McOrts/jaleometro/data/1002 Llogeta 7.jpeg

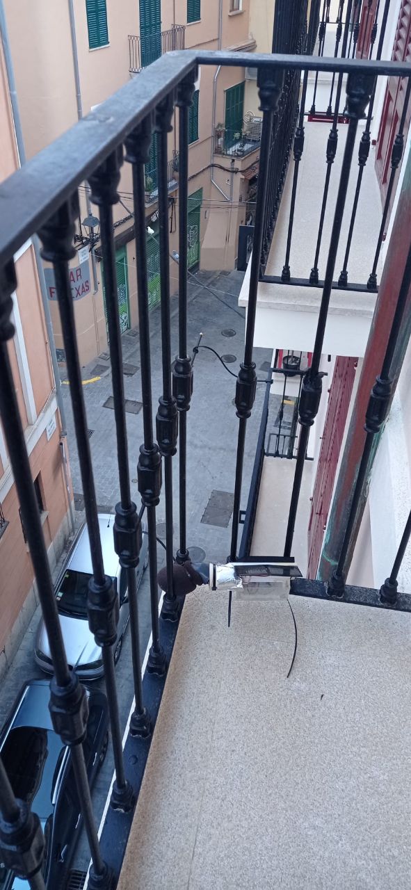
data/1002 Llogeta 7.jpeg
