McOrts/jaleometro/data/1004 Corderia 15-5_2.jpeg

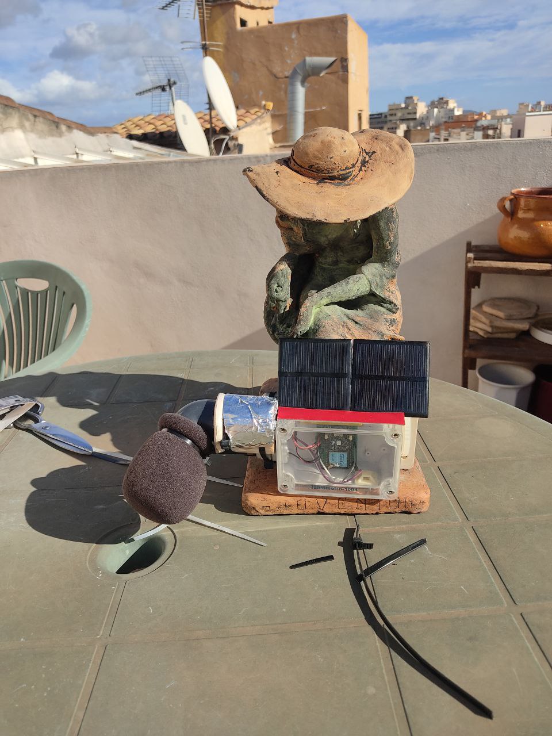
data/1004 Corderia 15-5_2.jpeg
