McOrts/jaleometro/data/1004 Corderia 15-5_3.jpeg

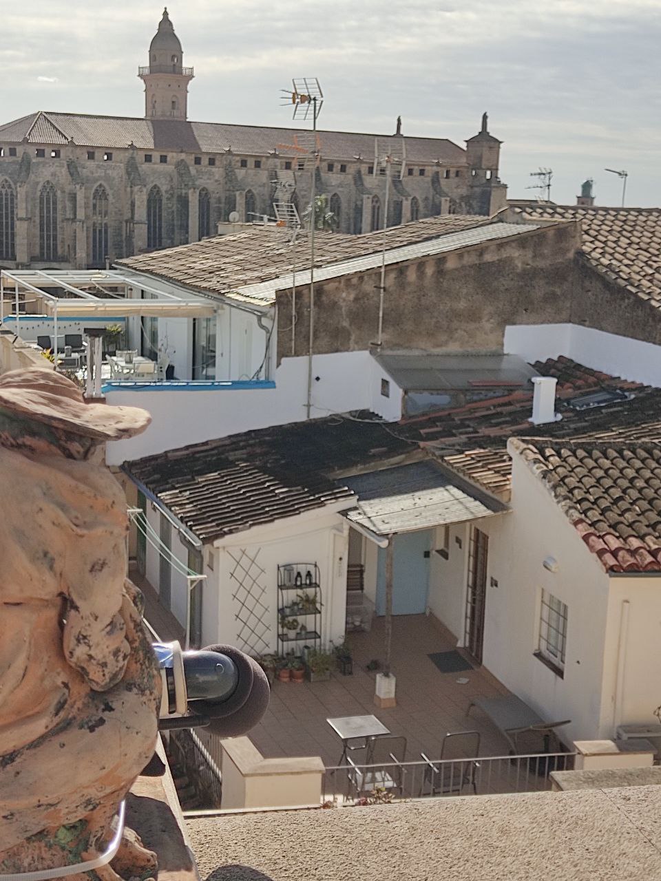
data/1004 Corderia 15-5_3.jpeg
