McOrts/jaleometro/data/1006 Cordería 15-1.jpeg

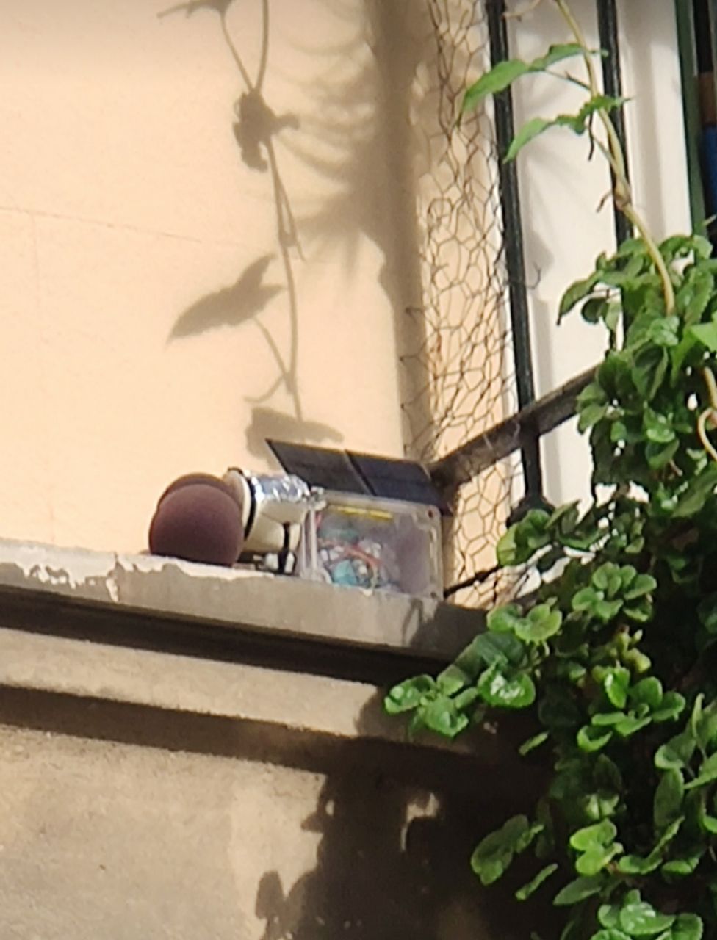
data/1006 Cordería 15-1.jpeg
