McOrts/jaleometro/data/1006 Cordería 15-1_2 copy.png

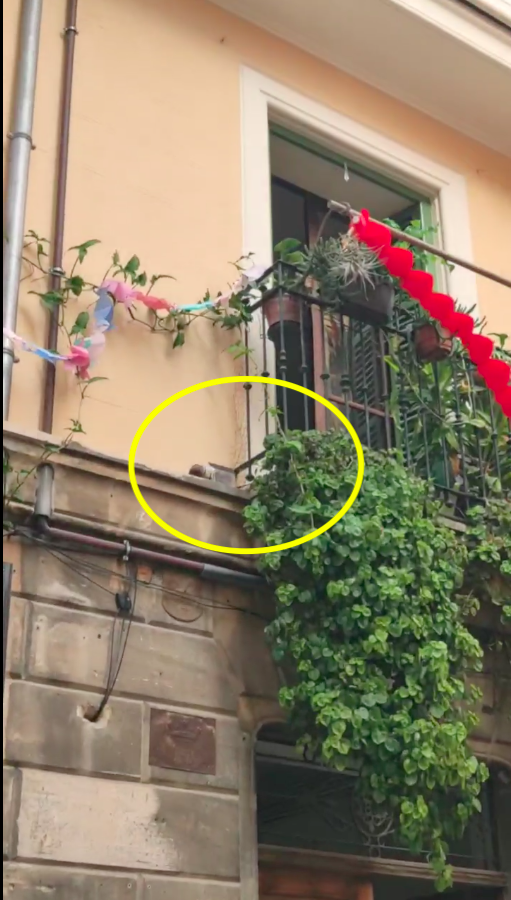
data/1006 Cordería 15-1_2 copy.png
