McOrts/jaleometro/doc/Microphone_Capsule_CEM-C9745JAD462P2.jpeg

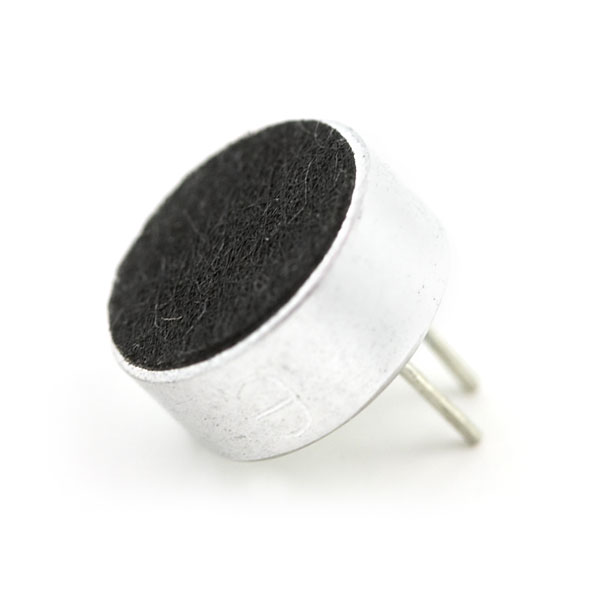
doc/Microphone_Capsule_CEM-C9745JAD462P2.jpeg
