McOrts/jaleometro/doc/MicrophoneWindscreen_foam .png

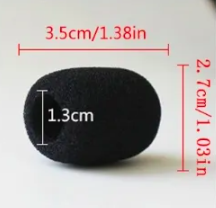
doc/MicrophoneWindscreen_foam .png
