McOrts/jaleometro/img/676x380.webp

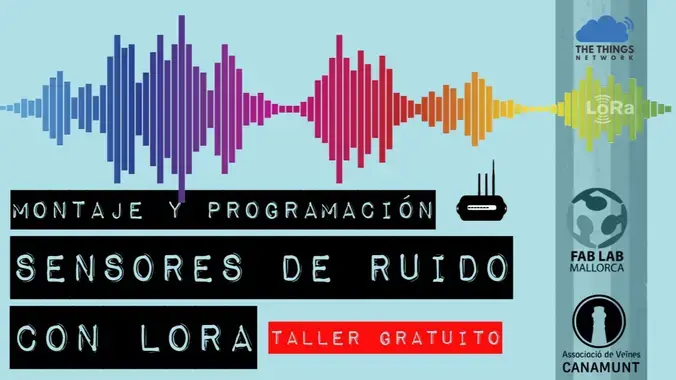
img/676x380.webp
