McOrts/jaleometro/img/1116.jpg

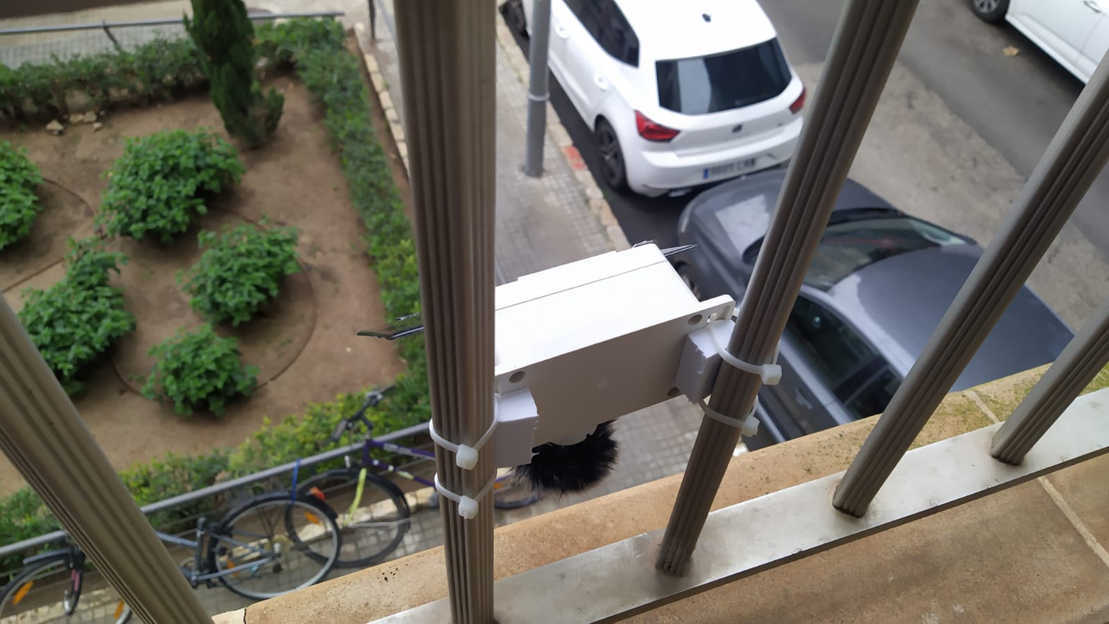
img/1116.jpg
