McOrts/jaleometro/img/canamunt_basemap.jpg

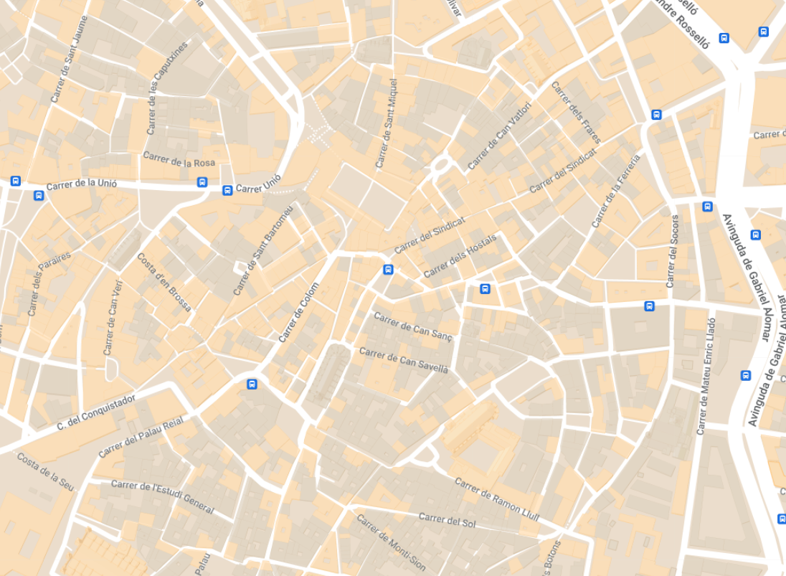
img/canamunt_basemap.jpg
