McOrts/jaleometro/img/DesviacionTipica.png

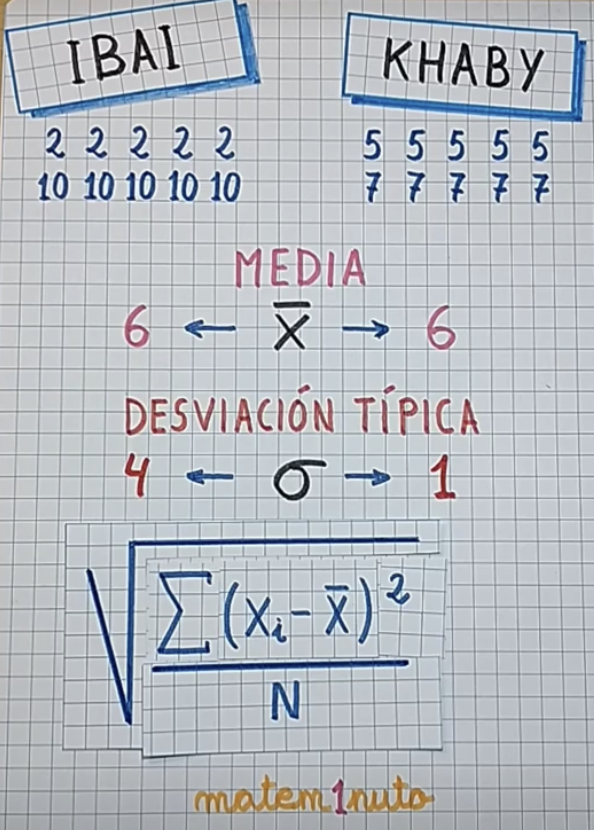
img/DesviacionTipica.png
