McOrts/jaleometro/img/How-Loud-Is-50-Decibels.jpg

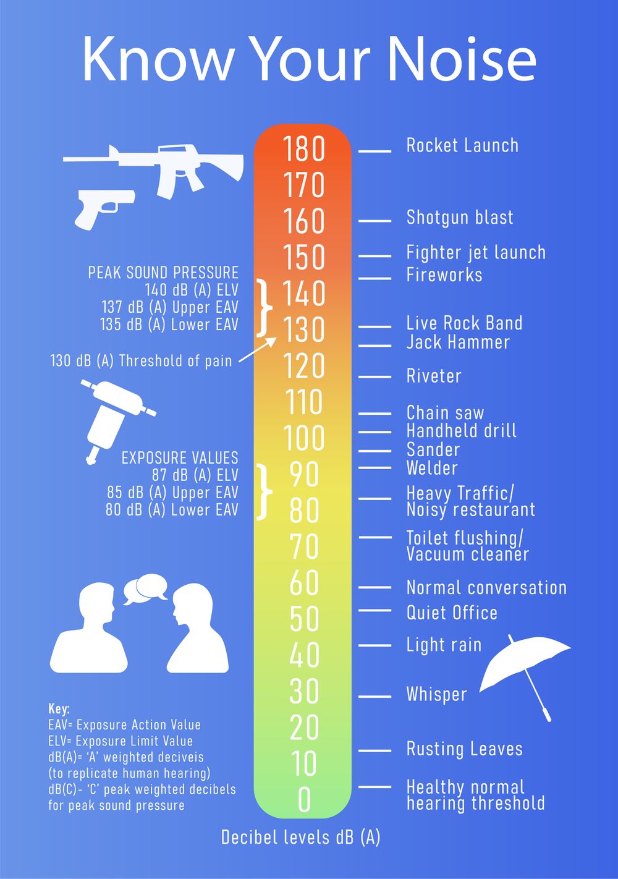
img/How-Loud-Is-50-Decibels.jpg
