McOrts/jaleometro/img/HTCC-AB01.png

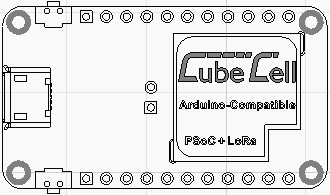
img/HTCC-AB01.png
