McOrts/jaleometro/img/IMG_3713.jpg

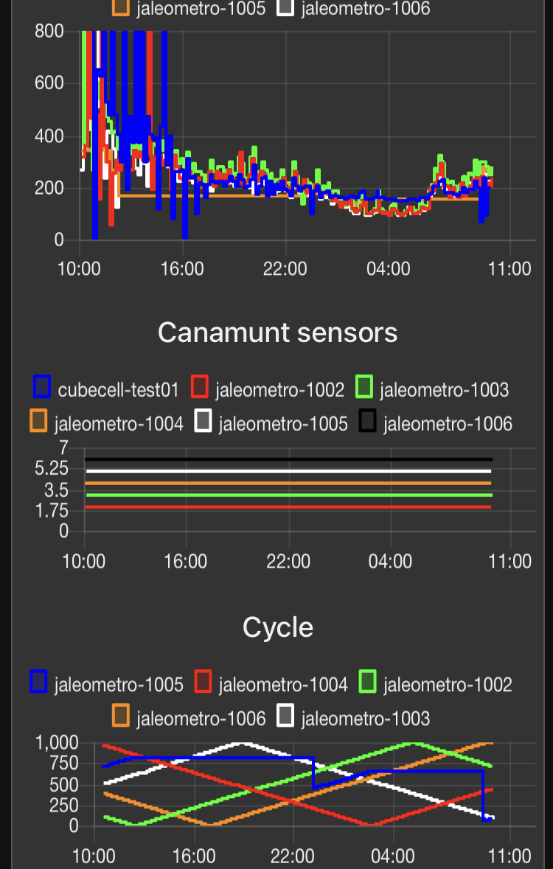
img/IMG_3713.jpg
