McOrts/jaleometro/img/jaleometro_0.jpg

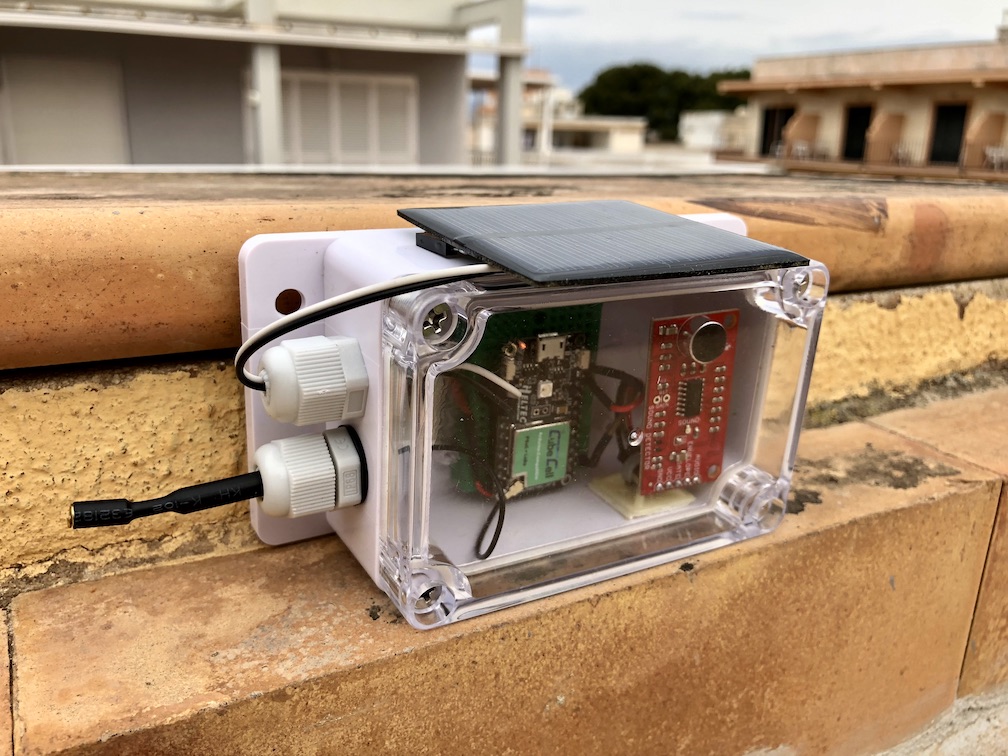
img/jaleometro_0.jpg
