McOrts/jaleometro/img/jaleometro_1.png

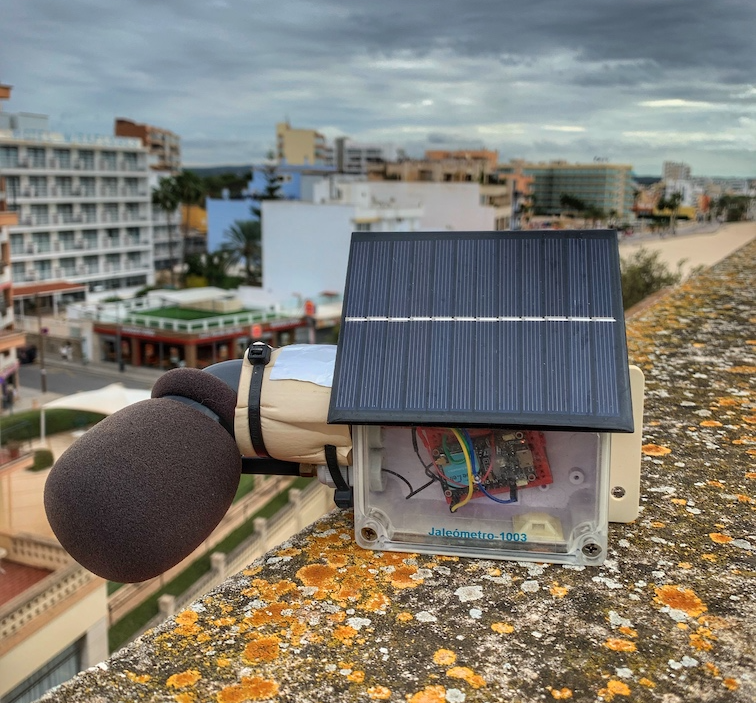
img/jaleometro_1.png
