McOrts/jaleometro/img/Jaleometro_1108.jpeg

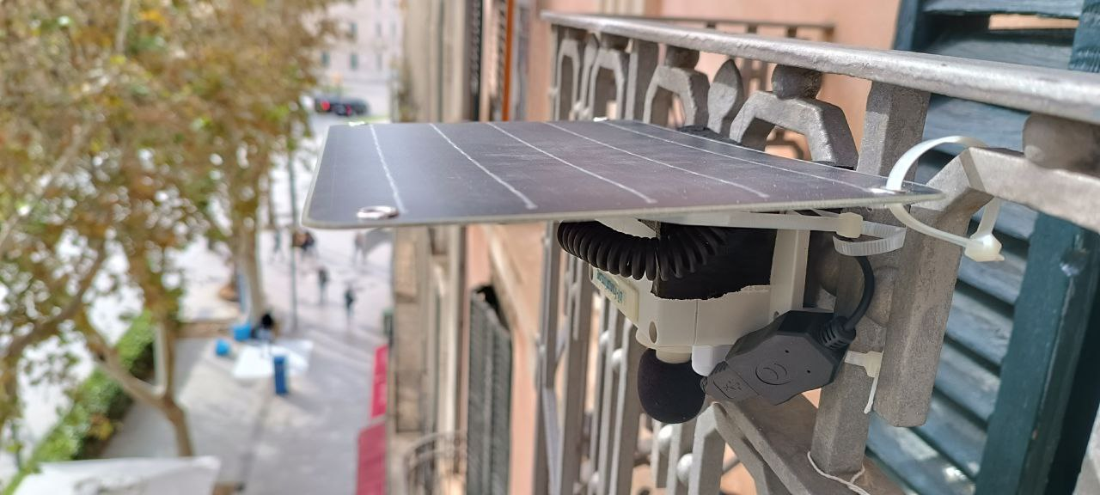
img/Jaleometro_1108.jpeg
