McOrts/jaleometro/img/JaleometroCollage.jpeg

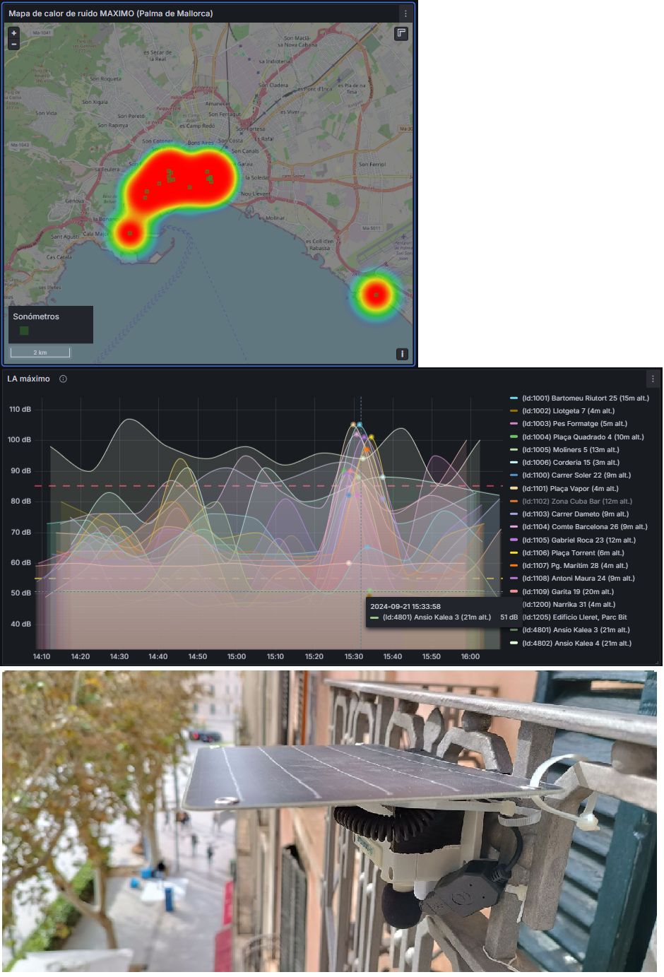
img/JaleometroCollage.jpeg
