McOrts/jaleometro/img/jaleometros_1.jpg

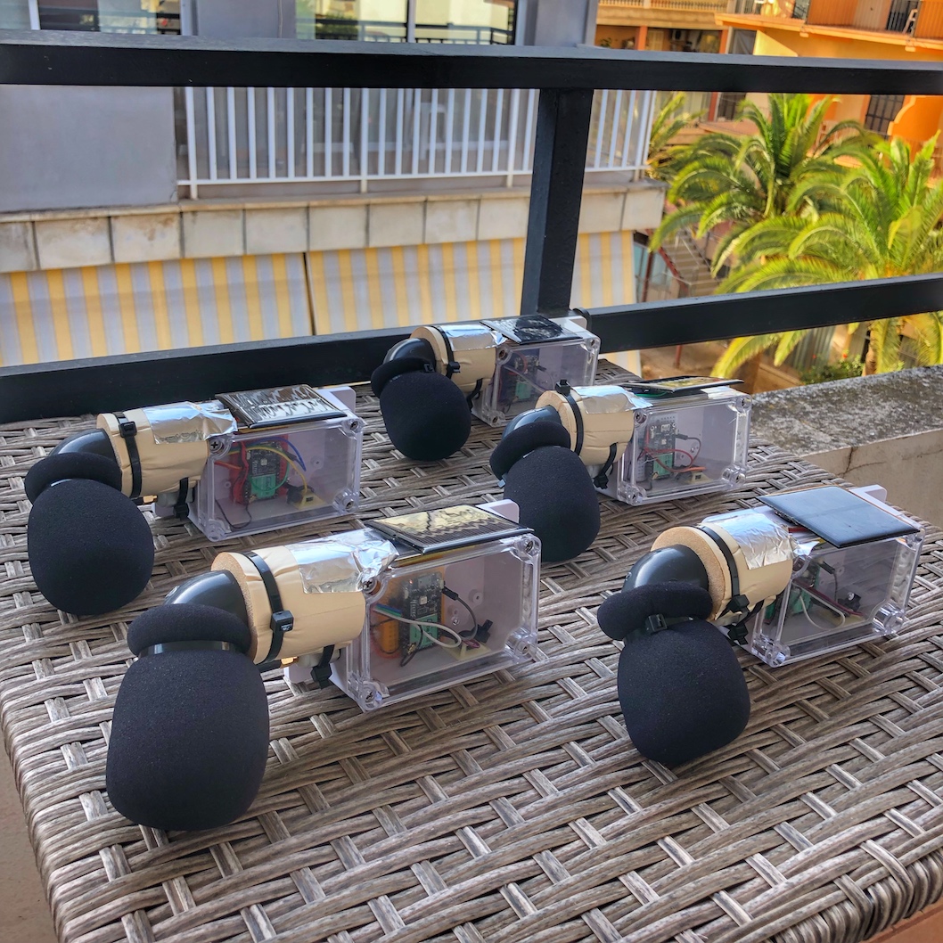
img/jaleometros_1.jpg
