McOrts/jaleometro/img/Jaleómetro_1200.jpg

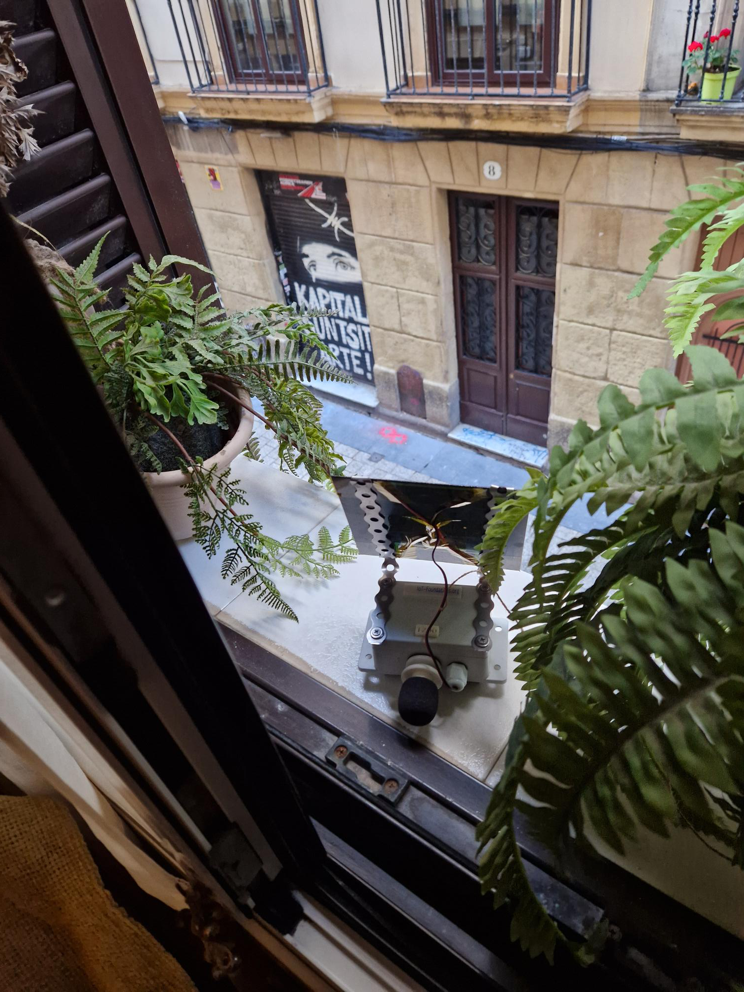
img/Jaleómetro_1200.jpg
