McOrts/jaleometro/img/TTN_device_OTAA.png

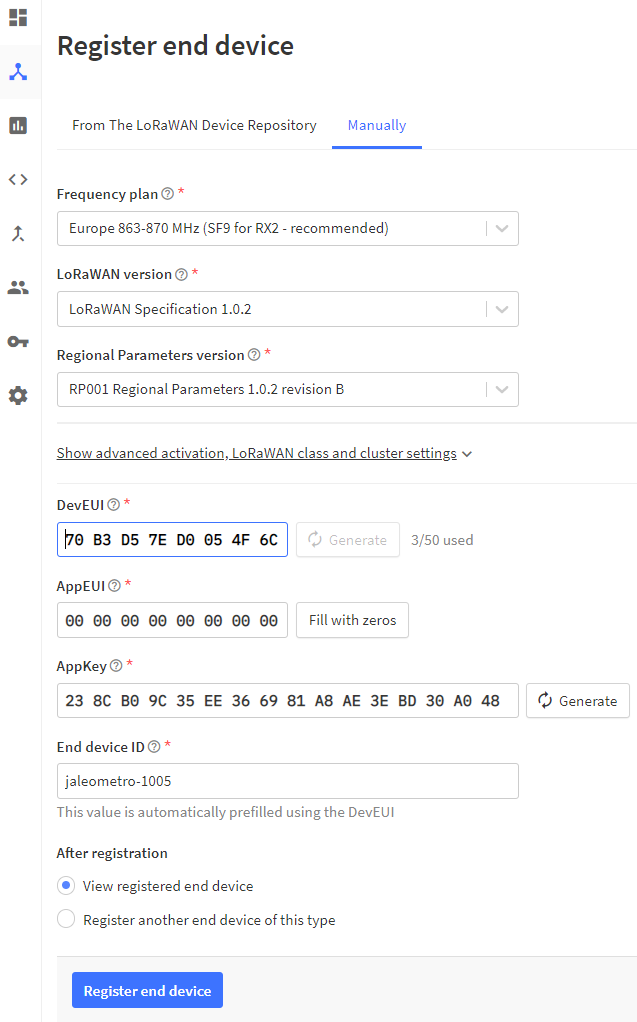
img/TTN_device_OTAA.png
