McOrts/jaleometro/news/8eed3acc-b989-45af-b673-5e21465e44ad.jpeg

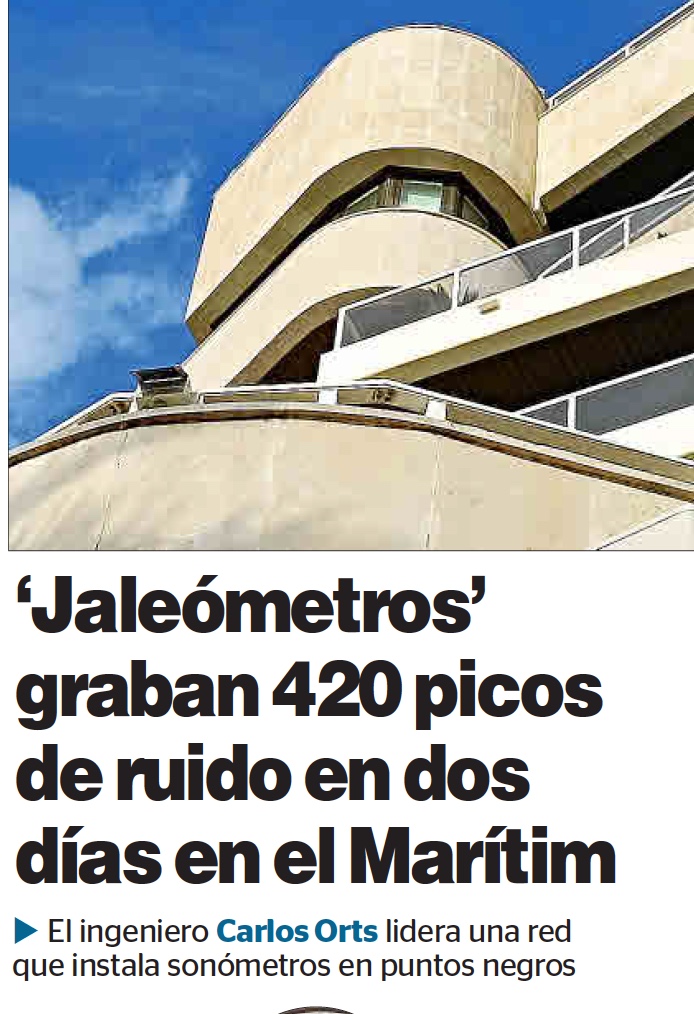
news/8eed3acc-b989-45af-b673-5e21465e44ad.jpeg
