McOrts/jaleometro/news/9c517f6d-d2a7-4473-ad57-f0665915687a.jpeg

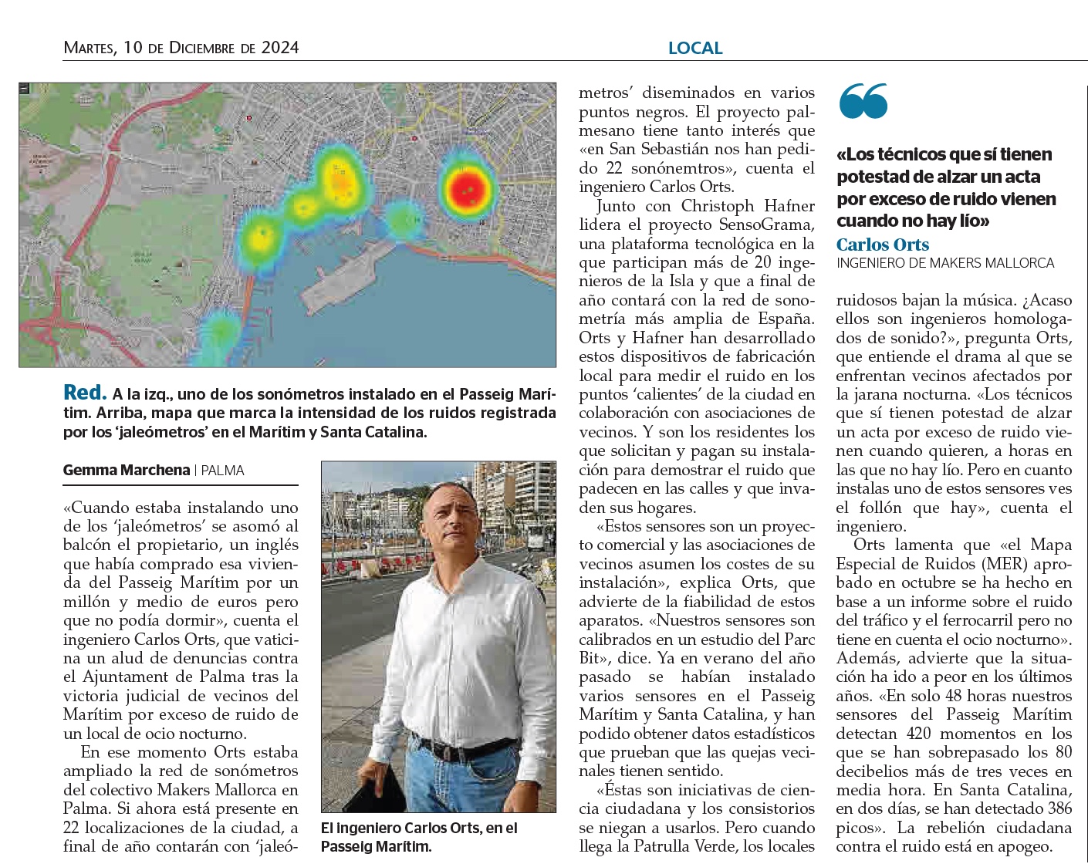
news/9c517f6d-d2a7-4473-ad57-f0665915687a.jpeg
