McOrts/jaleometro/news/APB_AAVVPaseoMaritimo_OK.jpeg

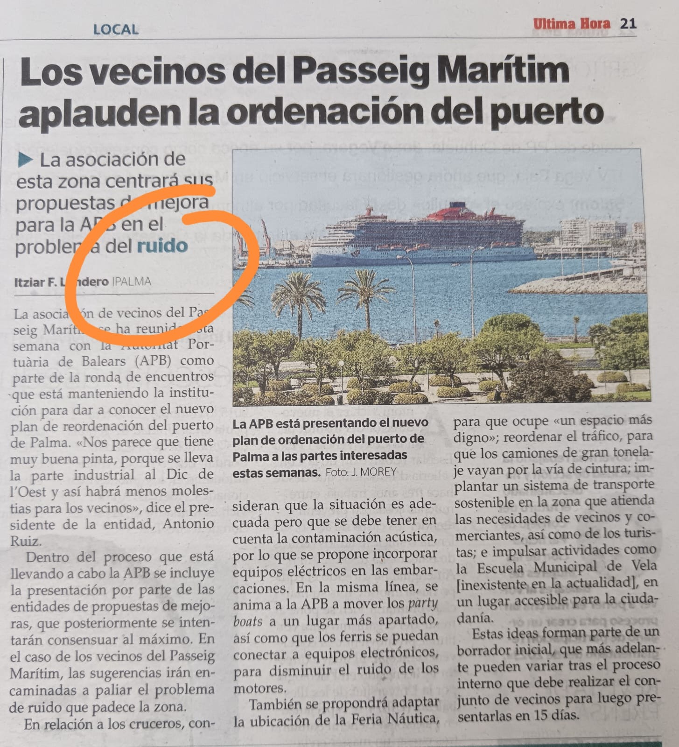
news/APB_AAVVPaseoMaritimo_OK.jpeg
