McOrts/jaleometro/news/Shamrock_ThreeLions_Cierre.jpeg

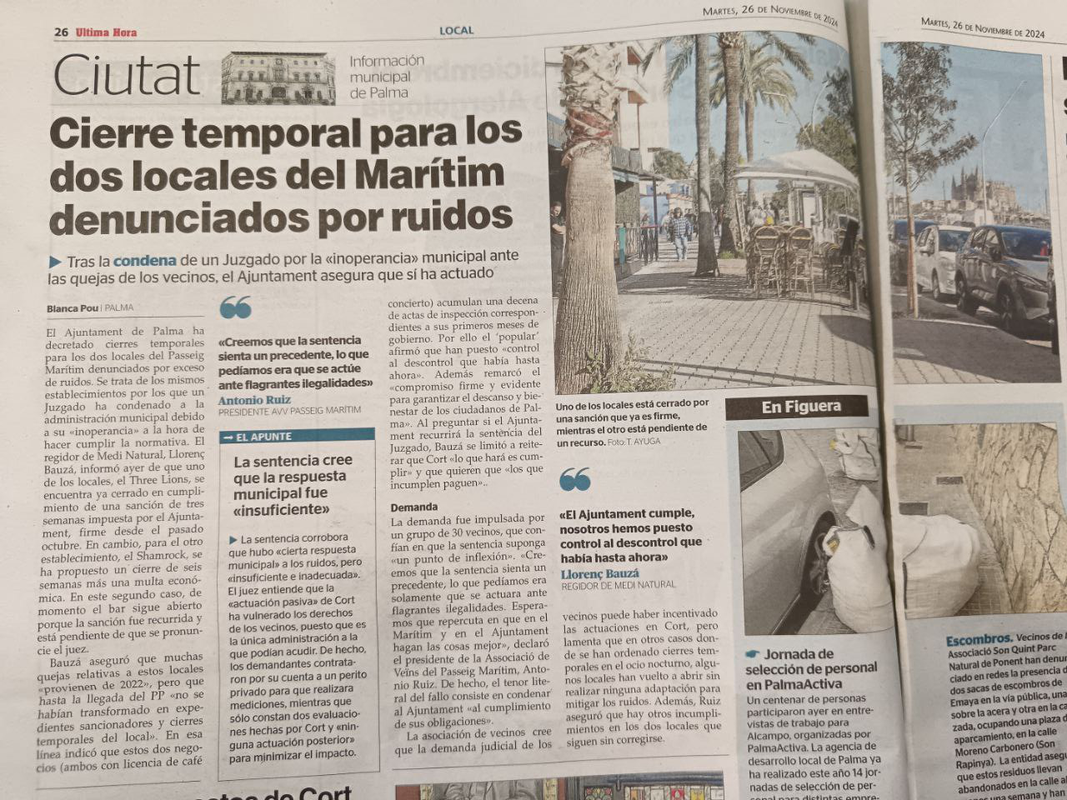
news/Shamrock_ThreeLions_Cierre.jpeg
