McOrts/jaleometro/PCB/jaleometro_v1_5_bb.png

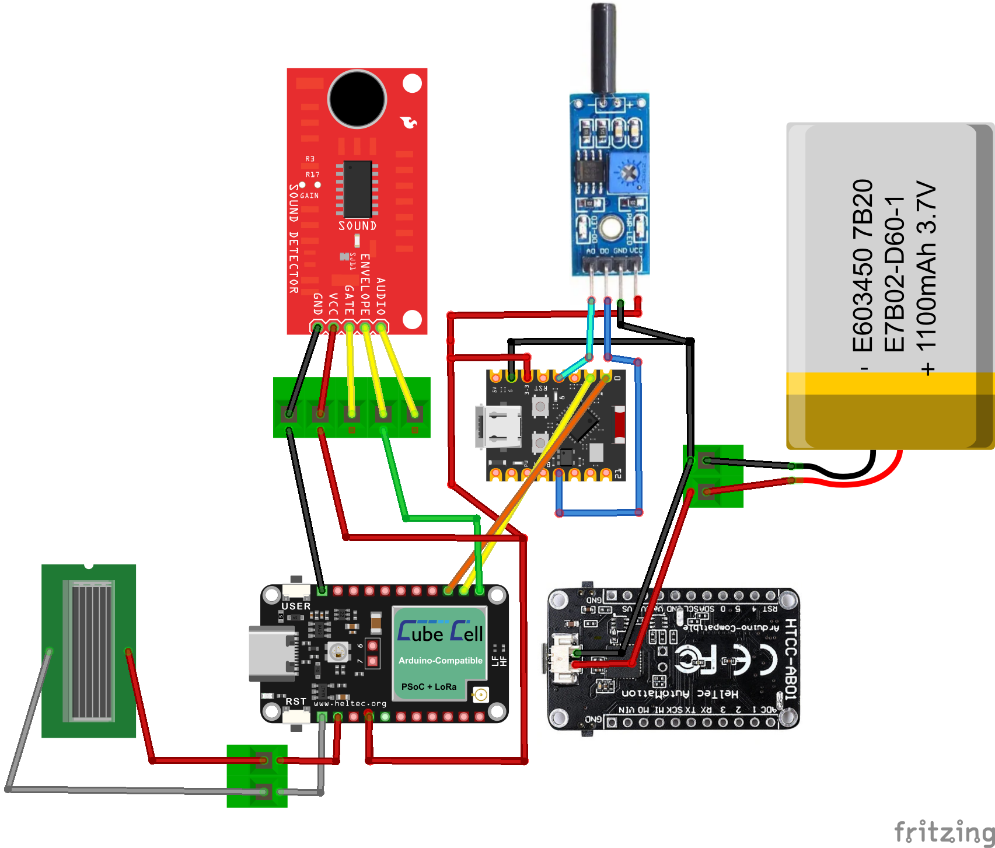
PCB/jaleometro_v1_5_bb.png
