McOrts/jaleometro/PCB/jaleometro_v1_5_pcb_dimensions.png

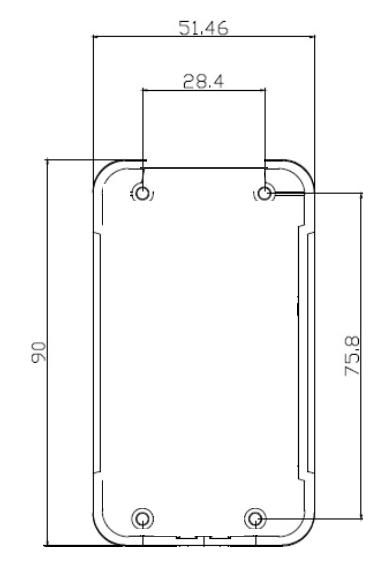
PCB/jaleometro_v1_5_pcb_dimensions.png
